andornaut/splinter-keyboard/scripts/panelize.py

#!/usr/bin/env python3
"""Combine the routed boards into one JLCPCB panel with KiKit.

Lays the input boards out in a single left-to-right row inside a frame, joins
each board to the frame with mouse-bite tabs, and adds corner fiducials and
tooling holes for assembly. Each board's references and nets are prefixed with
the board's file stem (e.g. left_D1, right_D1) so the two mirrored halves stay
unique in the position file / CPL. The panel inherits its boards' provenance stamp
(see provenance.py and `stamp` below).

Unlike the other scripts/*.py helpers this one needs more than the standard library
and pcbnew: KiKit (kikit.panelize). KiCad 10 support is only in
KiKit/pcbnewTransition git master (no PyPI release yet), so panelize.sh runs this
under a dedicated venv. inheritDrc=False is required: KiKit cannot merge the two
boards' net-class/DRC rules and aborts on save otherwise.

Usage: panelize.py <board.kicad_pcb> [more ...] --output panel.kicad_pcb [tuning flags]
"""

import argparse
import sys

# First, and marked so the import sort leaves it there: it silences pcbnew's
# startup wxASSERT by swapping fd 2 across the import, which only works if
# nothing has imported pcbnew yet. kikit below imports pcbnew itself.
from lib.pcbnew_quiet import pcbnew  # isort: skip

from pathlib import Path

from kikit.panelize import Origin, Panel
from kikit.units import mm
from lib.provenance import read_stamp, write_stamp


def stem(path):
    return Path(path).stem


def build(
    boards,
    output,
    rail,
    gap,
    frame_space,
    tabs,
    tab_width,
    mb_diameter,
    mb_spacing,
    tab_min_distance,
):
    panel = Panel(output)

    # Lay the boards out in one row, each placed by its top-left corner, with a
    # gap between neighbours. Prefix refs/nets per board so the mirrored halves
    # do not collide in the pos file / CPL.
    x = 0
    for f in boards:
        pre = stem(f)
        # appendBoard returns the placed board's Edge.Cuts bounding box, so the
        # next board's x-advance reuses it instead of re-loading f from disk.
        bbox = panel.appendBoard(
            f,
            pcbnew.VECTOR2I(x, 0),
            origin=Origin.TopLeft,
            refRenamer=lambda _n, r, pre=pre: f"{pre}_{r}",
            netRenamer=lambda _n, net, pre=pre: f"{pre}_{net}",
            inheritDrc=False,
        )
        x += bbox.GetWidth() + gap

    # Frame (rails on all four sides) + mouse-bite tabs joining boards to it.
    panel.makeFrame(widthH=rail, widthV=rail, hspace=frame_space, vspace=frame_space)
    panel.buildPartitionLineFromBB()
    panel.buildTabAnnotationsFixed(tabs, tabs, tab_width, tab_width, tab_min_distance, [])
    cuts = panel.buildTabsFromAnnotations(0)
    panel.makeMouseBites(cuts, diameter=mb_diameter, spacing=mb_spacing)

    # Assembly aids on the rails: fiducials for optical alignment, tooling holes
    # for the pick-and-place. Offsets keep them within the rail width.
    panel.addCornerFiducials(4, rail, rail, 1 * mm, 2 * mm)
    panel.addCornerTooling(4, rail, rail, 1.5 * mm)

    panel.save()


def stamp(boards, output):
    """Carry the source boards' provenance stamp onto the panel.

    Inherited, never rebuilt. A panel is its boards merged and nothing else, so the
    stamp that describes it is the one they already carry. Building a fresh one here
    would re-read the working tree at panel time, which is always later than the
    boards were stamped and, in a pipeline run, always after the steps that rewrite
    the boards have dirtied it: the panel would report clean=no beside the very
    commit its copper came from, and the commit field would read as meaningless.

    Boards that disagree is a hard error. A panel merged from two generations of
    board has no single provenance, and reporting either one of them would be a
    claim about copper that is not all there.
    """
    stamps = [(stem(f), read_stamp(pcbnew.LoadBoard(f))) for f in boards]
    missing = [name for name, text in stamps if not text]
    if missing:
        sys.exit(
            f"ERROR {', '.join(missing)}: no provenance stamp, re-run the pipeline to stamp the boards, then panel them"
        )
    if len({text for _, text in stamps}) > 1:
        listing = "\n".join(f"    {name}: {text}" for name, text in stamps)
        sys.exit(
            "ERROR: the boards carry different provenance stamps, so the panel has "
            f"no single provenance to report:\n{listing}\n"
            "    Re-run the pipeline so every half is built in one run"
        )
    text = stamps[0][1]
    board = pcbnew.LoadBoard(output)
    write_stamp(board, text)
    board.Save(output)
    print(f"  stamped {output}: {text}")


def main():
    ap = argparse.ArgumentParser(description=__doc__)
    ap.add_argument("board", nargs="+", help="routed .kicad_pcb file(s), laid out left-to-right")
    ap.add_argument("--output", required=True, help="output panel .kicad_pcb path")
    ap.add_argument("--rail", type=float, default=5.0, help="frame rail width, mm (default 5)")
    ap.add_argument("--gap", type=float, default=3.0, help="gap between boards, mm (default 3)")
    ap.add_argument(
        "--frame-space",
        type=float,
        default=3.0,
        help="board-to-frame gap, mm (default 3)",
    )
    ap.add_argument("--tabs", type=int, default=2, help="tabs per board edge (default 2)")
    ap.add_argument("--tab-width", type=float, default=3.0, help="tab width, mm (default 3)")
    ap.add_argument(
        "--mousebite-diameter",
        type=float,
        default=0.5,
        help="mouse-bite hole diameter, mm",
    )
    ap.add_argument(
        "--mousebite-spacing",
        type=float,
        default=0.9,
        help="mouse-bite hole spacing, mm",
    )
    ap.add_argument(
        "--tab-min-distance",
        type=float,
        default=8.0,
        help="min distance between tabs, mm",
    )
    args = ap.parse_args()

    if len(args.board) < 2:
        sys.exit("ERROR: panelize needs at least 2 boards (left + right)")
    for f in args.board:
        if not Path(f).is_file():
            sys.exit(f"ERROR {f}: no such board")

    # KiCad internal units are integer nanometres; mm scales up, so round to int
    # (argparse gives floats) before these reach pcbnew/KiKit geometry calls.
    def nm(v):
        return round(v * mm)

    Path(args.output).resolve().parent.mkdir(parents=True, exist_ok=True)
    build(
        args.board,
        args.output,
        rail=nm(args.rail),
        gap=nm(args.gap),
        frame_space=nm(args.frame_space),
        tabs=args.tabs,
        tab_width=nm(args.tab_width),
        mb_diameter=nm(args.mousebite_diameter),
        mb_spacing=nm(args.mousebite_spacing),
        tab_min_distance=nm(args.tab_min_distance),
    )

    stamp(args.board, args.output)


if __name__ == "__main__":
    main()
